peterzimon/shmoergh-a1-prototype/vco/plots/PDF/waveshaper-A-B_Cu.pdf

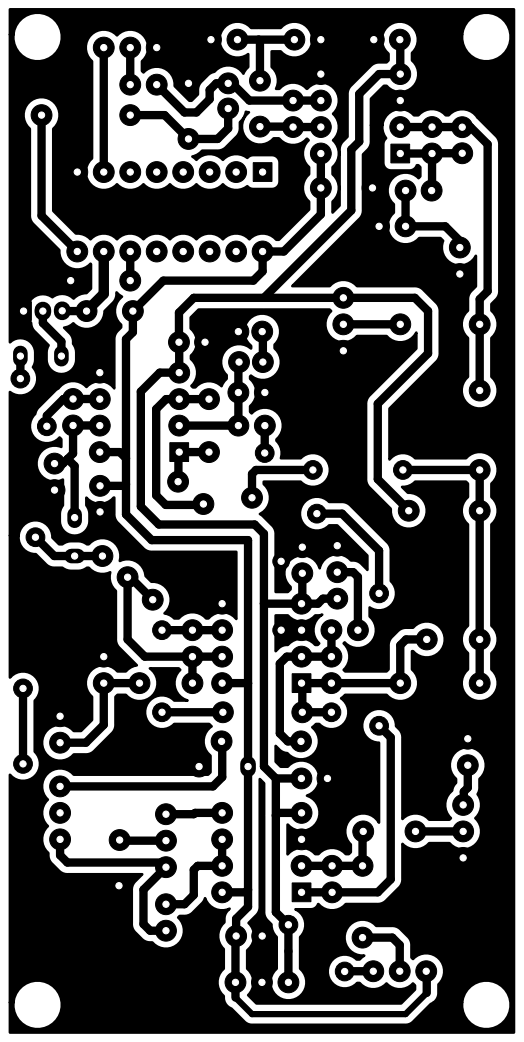
[picture p35: page 1]
