peterzimon/shmoergh-a1-prototype/vco/plots/PDF/waveshaper-B-B_Cu.pdf

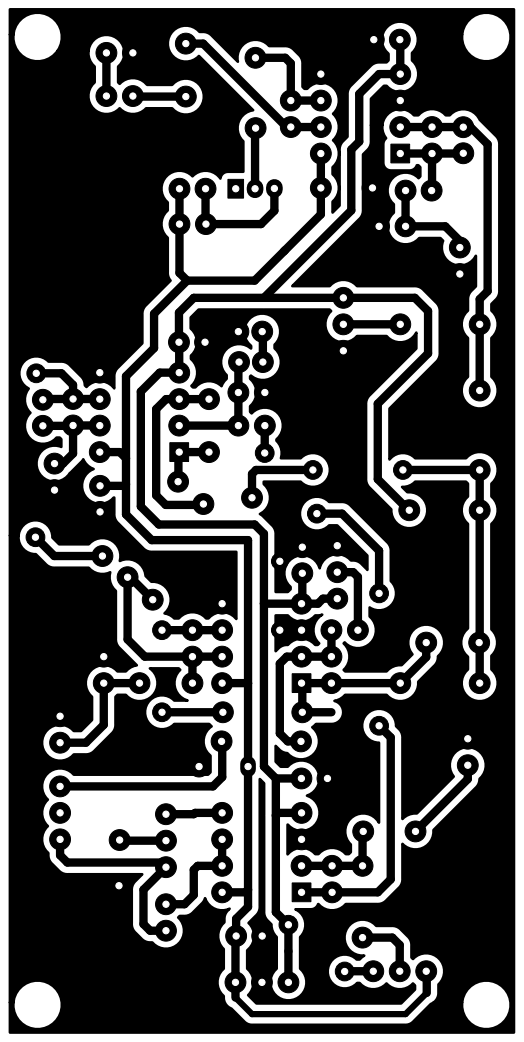
[picture p36: page 1]
