peterzimon/shmoergh-a1-prototype/adsr/plots/PDF/adsr-B_Cu.pdf

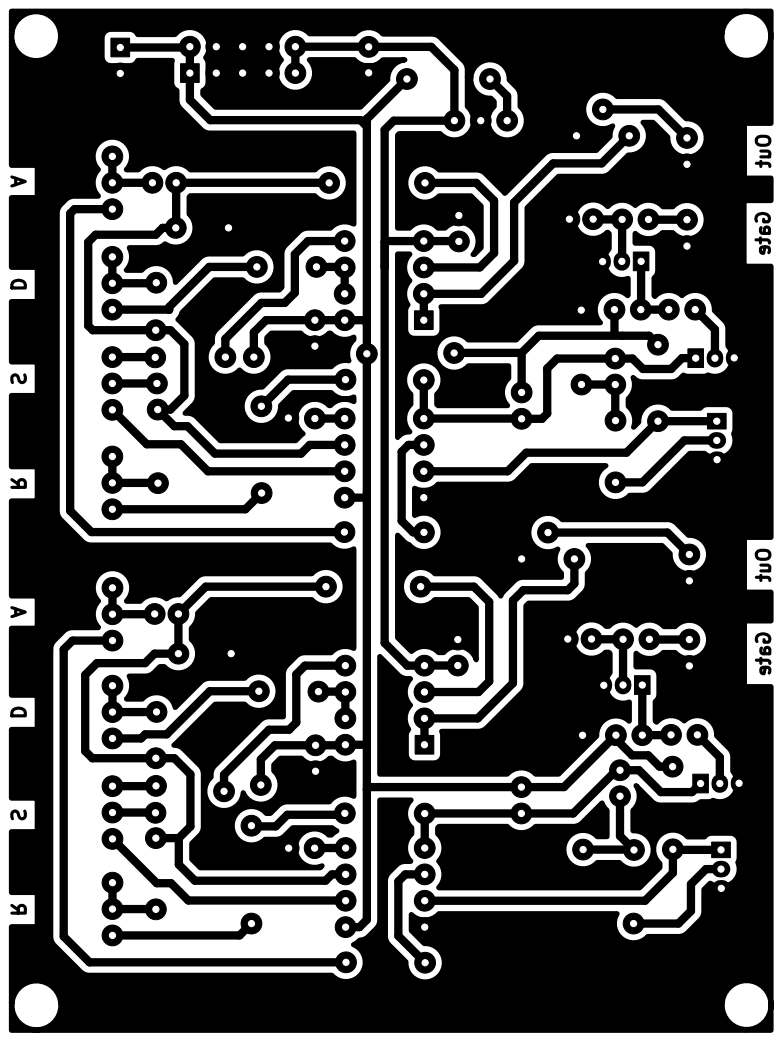
[picture p37: page 1]

Out Gate Out Gate R S D A R S D A
