peterzimon/shmoergh-a1-prototype/mixer-lfo-glide-output/plots/PDF/mixer-lfo-glide-output-B_Cu.pdf

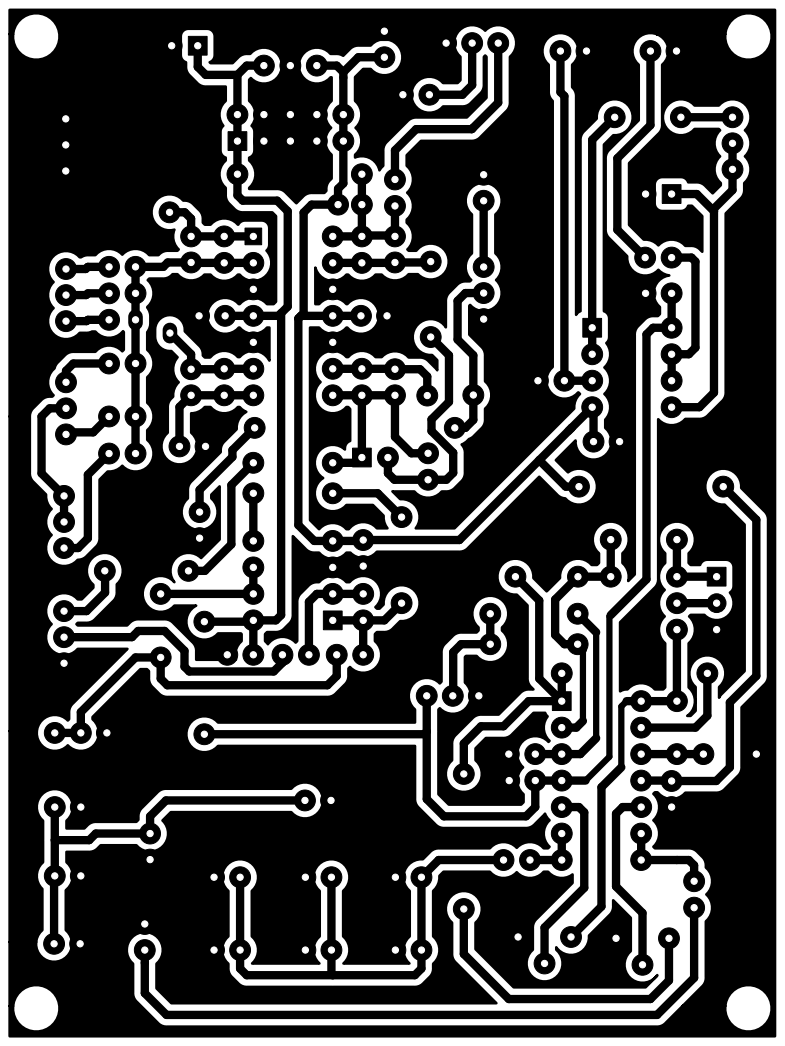
[picture p38: page 1]
