peterzimon/shmoergh-a1-prototype/modmixer/plots/PDF/modmixer-B_Cu.pdf

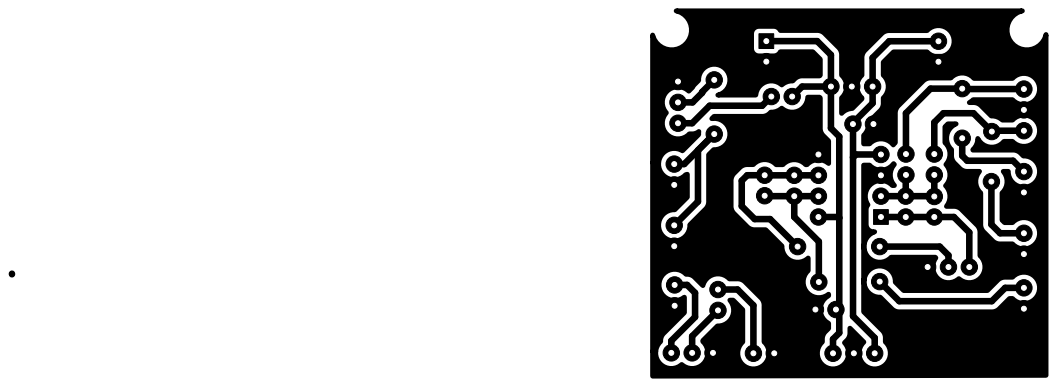
[picture p39: page 1]
