peterzimon/shmoergh-a1-prototype/psu/plots/PDF/psu-B_Cu.pdf

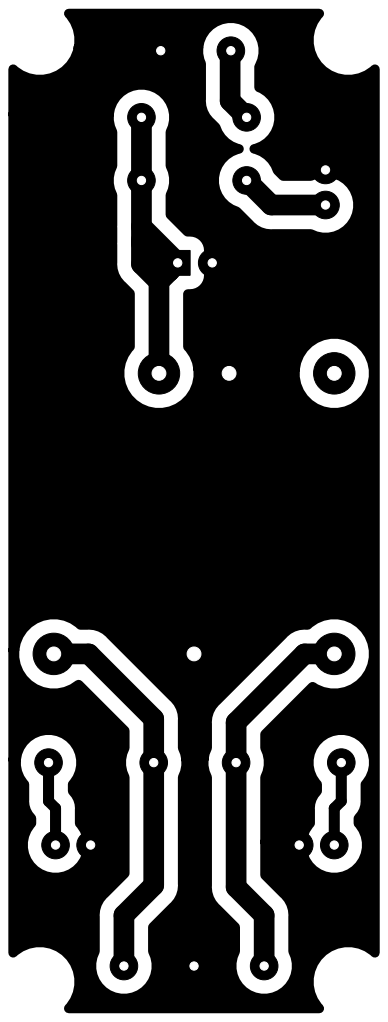
[picture p40: page 1]
