peterzimon/shmoergh-a1-prototype/vca-ota/plots/PDF/vca-ota-F_Cu.pdf

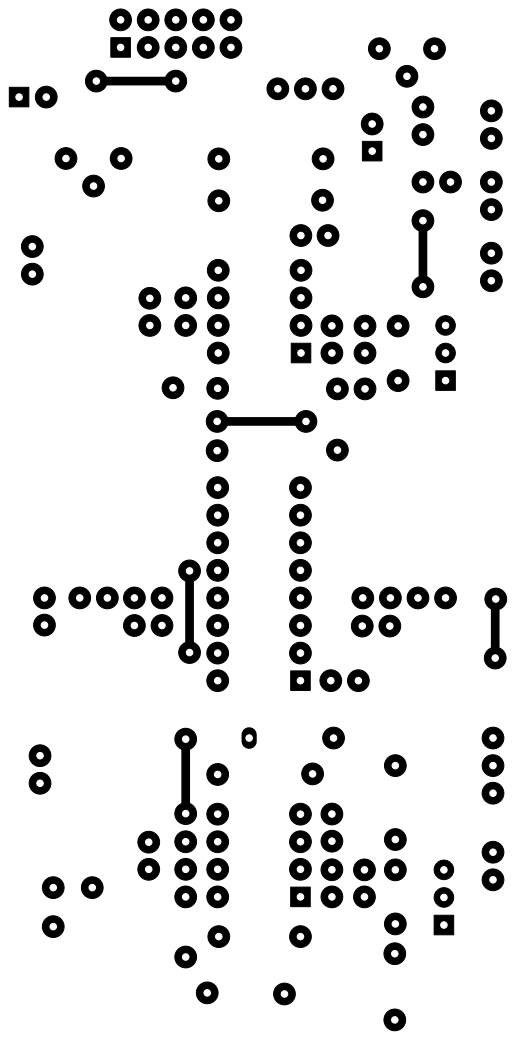
[picture p41: page 1]
