peterzimon/shmoergh-a1-prototype/vca-transistor/plots/PDF/vca-transistor-B_Cu.pdf

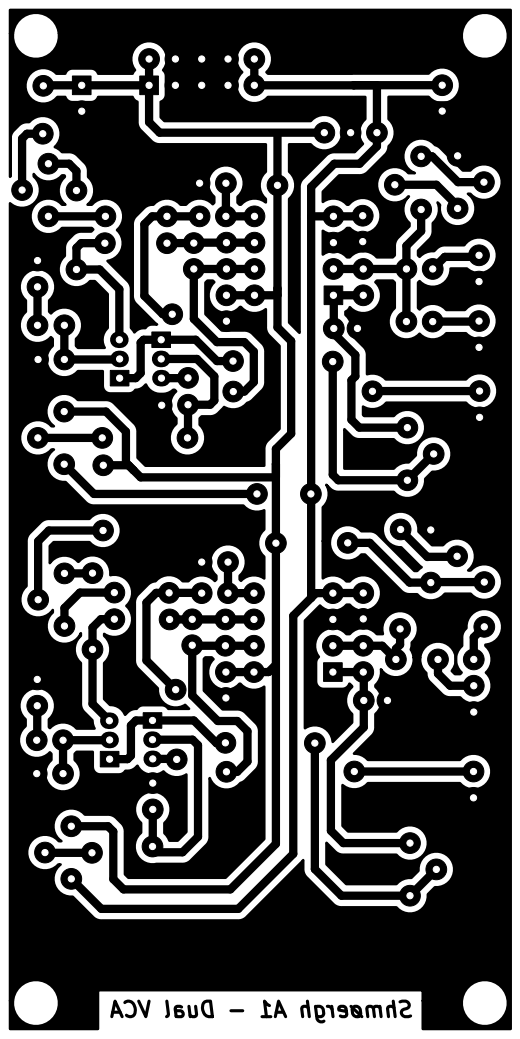
[picture p42: page 1]
