peterzimon/shmoergh-a1-prototype/vcf-diode-ladder/plots/PDF/vca-diode-ladder-B_Cu.pdf

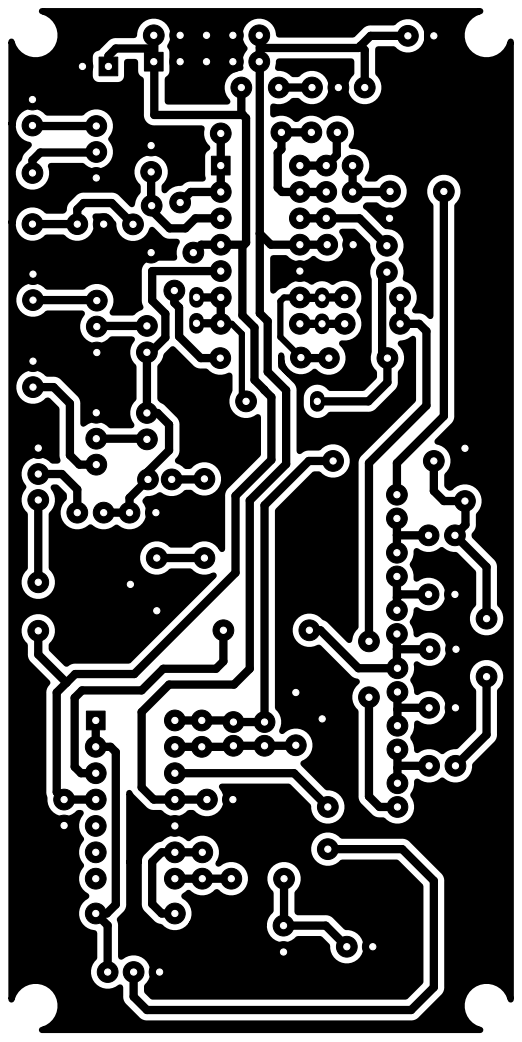
[picture p43: page 1]
